ZelTroN-2k3/arduino-cibi-vfo/img/config_menu_06.jpg

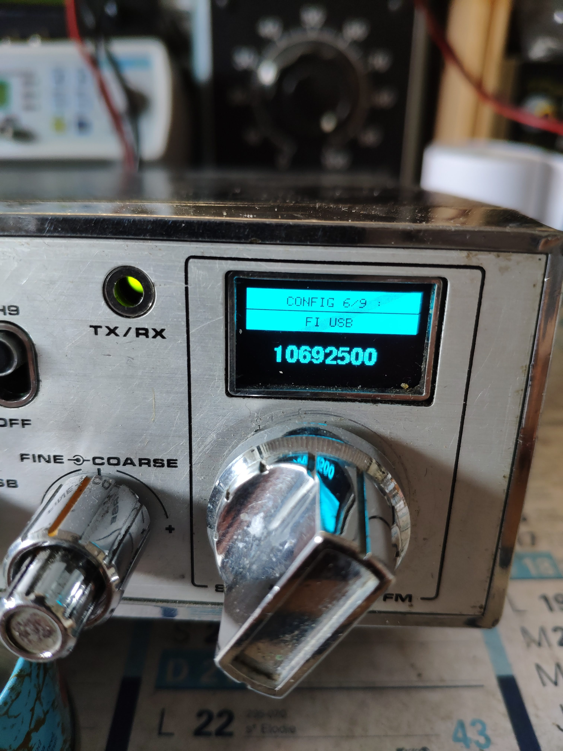
img/config_menu_06.jpg
