ZelTroN-2k3/arduino-cibi-vfo/img/config_menu_07.jpg

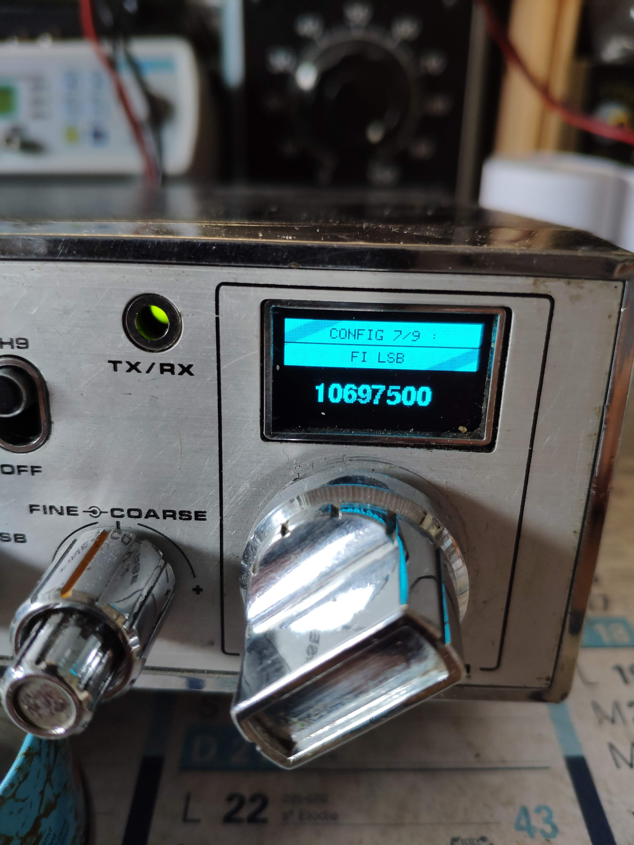
img/config_menu_07.jpg
