ZelTroN-2k3/arduino-cibi-vfo/img/main_menu_clarifier_fine.jpg

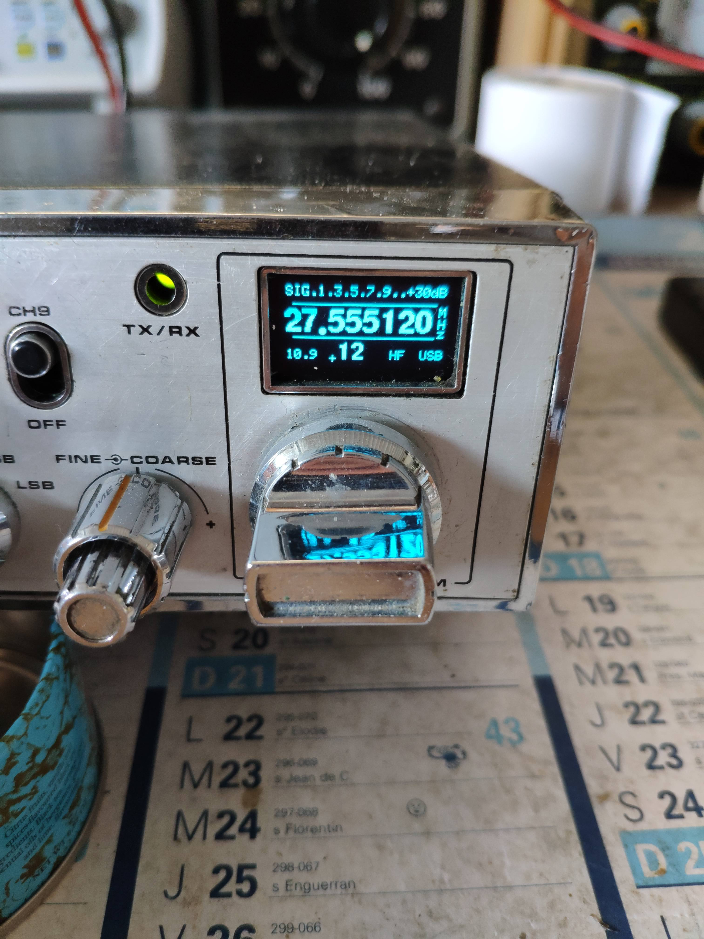
img/main_menu_clarifier_fine.jpg
