ZelTroN-2k3/arduino-cibi-vfo/img/main_menu_smeter_01.jpg

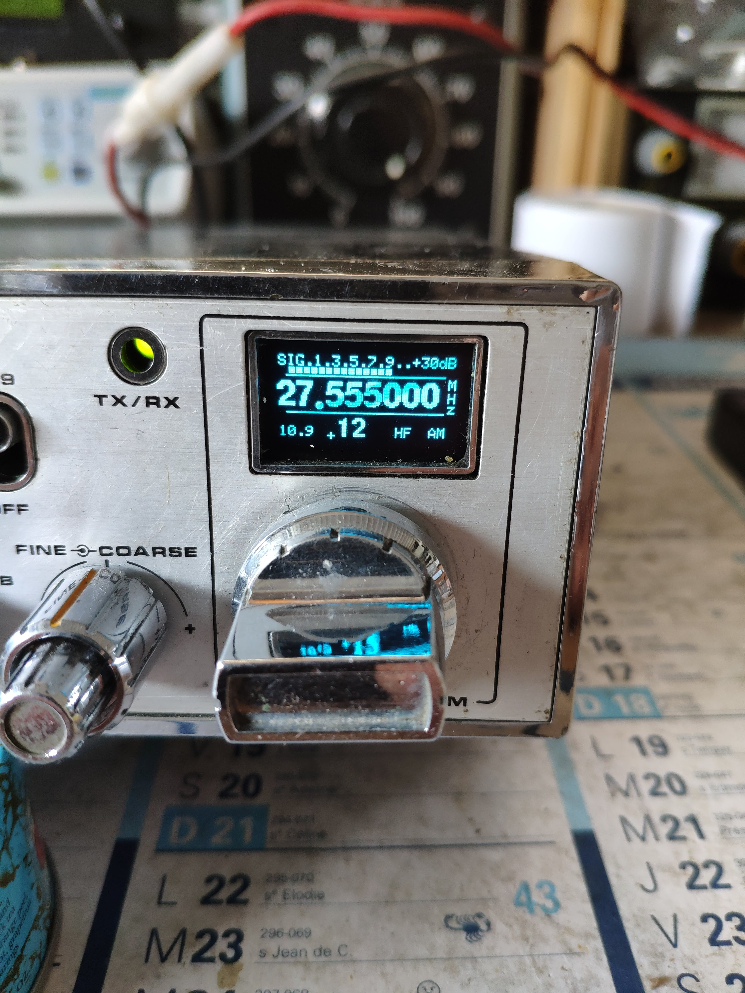
img/main_menu_smeter_01.jpg
