ZelTroN-2k3/arduino-cibi-vfo/img/main_menu_smeter_02.jpg

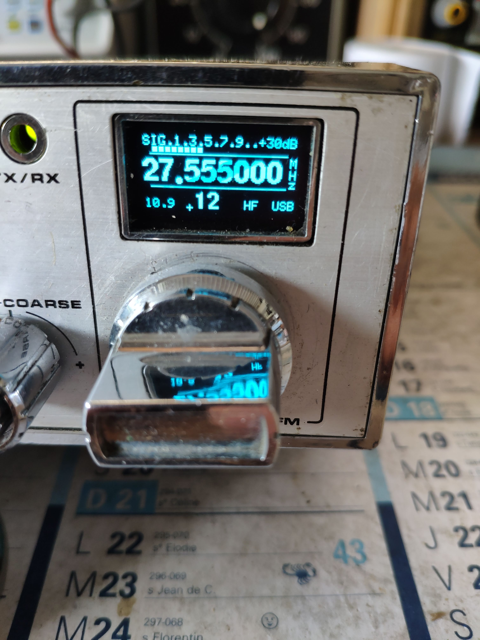
img/main_menu_smeter_02.jpg
