ZelTroN-2k3/arduino-cibi-vfo/src/config.cpp

/*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
 * * Redistributions of source code must retain the above copyright
 *   notice, this list of conditions and the following disclaimer.
 * * Redistributions in binary form must reproduce the above copyright
 *   notice, this list of conditions and the following disclaimer in the
 *   documentation and/or other materials provided with the distribution.
 * * Neither the name of the author Vincent Hervieux, nor the
 *   names of its contributors may be used to endorse or promote products
 *   derived from this software without specific prior written permission.
 *
 * THIS SOFTWARE IS PROVIDED BY THE REGENTS AND CONTRIBUTORS ``AS IS'' AND ANY
 * EXPRESS OR IMPLIED WARRANTIES, INCLUDING, BUT NOT LIMITED TO, THE IMPLIED
 * WARRANTIES OF MERCHANTABILITY AND FITNESS FOR A PARTICULAR PURPOSE ARE
 * DISCLAIMED. IN NO EVENT SHALL THE REGENTS AND CONTRIBUTORS BE LIABLE FOR ANY
 * DIRECT, INDIRECT, INCIDENTAL, SPECIAL, EXEMPLARY, OR CONSEQUENTIAL DAMAGES
 * (INCLUDING, BUT NOT LIMITED TO, PROCUREMENT OF SUBSTITUTE GOODS OR SERVICES;
 * LOSS OF USE, DATA, OR PROFITS; OR BUSINESS INTERRUPTION) HOWEVER CAUSED AND
 * ON ANY THEORY OF LIABILITY, WHETHER IN CONTRACT, STRICT LIABILITY, OR TORT
 * (INCLUDING NEGLIGENCE OR OTHERWISE) ARISING IN ANY WAY OUT OF THE USE OF THIS
 * SOFTWARE, EVEN IF ADVISED OF THE POSSIBILITY OF SUCH DAMAGE.
 */

#include "config.h"
#include "utils.h"
#include "vfo.h"

#include <avr/eeprom.h>

const static uint32_t EEPROM_HEADER         PROGMEM =  0xDEADBEEF;
const static uint32_t DEFAULT_CIBI_FREQ     PROGMEM =  27555000;
const static uint32_t DEFAULT_CIBI_MIN_FREQ PROGMEM =  25000000;
const static uint32_t DEFAULT_CIBI_MAX_FREQ PROGMEM =  30000000;
const static uint32_t DEFAULT_FREQ_STEP_INC PROGMEM =  5000;
/* On superstar 3900 and derivated:
  - reference oscillator is at 10240KHz
  - FI is either 10695KHz(CW,AM,FM), 10692.5KHz(USB), 10697.5KHz(LSB) */
const static uint32_t DEFAULT_FI_FREQ_AM PROGMEM = 10695000;
const static uint32_t DEFAULT_FI_FREQ_USB PROGMEM = 10692500;
const static uint32_t DEFAULT_FI_FREQ_LSB PROGMEM = 10697500;
const static  int32_t DEFAULT_VFO_ADJ PROGMEM = 0; 
const static  int32_t DEFAULT_CLARIFIER_ADJ PROGMEM = 0; 
const static  int32_t DEFAULT_SMETER_ADJ PROGMEM = 0; 
Config::Config(Input &_input, U8G2 &_display, DDS &_dds):
context_({ 
  .eeprom_header = EEPROM_HEADER,
  .cibi_frequency = DEFAULT_CIBI_FREQ,
  .cibi_min_freq = DEFAULT_CIBI_MIN_FREQ,
  .cibi_max_freq = DEFAULT_CIBI_MAX_FREQ,
  .freq_step_inc = DEFAULT_FREQ_STEP_INC,
  .fi_am = DEFAULT_FI_FREQ_AM,
  .fi_usb = DEFAULT_FI_FREQ_USB,
  .fi_lsb = DEFAULT_FI_FREQ_LSB,
  .vfo_adj = DEFAULT_VFO_ADJ,
  .clarifier_adj = DEFAULT_CLARIFIER_ADJ,
  .smeter_adj = DEFAULT_SMETER_ADJ
}),
input_(_input),
dds_(_dds),
current_cursor_pos_(CURSOR_POS_NONE),
current_menu_index_(CONFIG_CIBI_FREQ),
current_value_(&context_.cibi_frequency)
{
  view_ = new ConfigDisplay(_display);
}

Config::Config(const Config& _config) :
context_({ 
  .eeprom_header = _config.context_.eeprom_header,
  .cibi_frequency = _config.context_.cibi_frequency,
  .cibi_min_freq = _config.context_.cibi_min_freq,
  .cibi_max_freq = _config.context_.cibi_max_freq,
  .freq_step_inc = _config.context_.freq_step_inc,
  .fi_am = _config.context_.fi_am,
  .fi_usb = _config.context_.fi_usb,
  .fi_lsb = _config.context_.fi_lsb,
  .vfo_adj = _config.context_.vfo_adj,
  .clarifier_adj = _config.context_.clarifier_adj,
  .smeter_adj = _config.context_.smeter_adj,
}),
input_(_config.input_),
dds_(_config.dds_),
view_(_config.view_),
current_cursor_pos_(_config.current_cursor_pos_),
current_menu_index_(_config.current_menu_index_),
current_value_(_config.current_value_)
{

}

Config::~Config()
{
  delete view_;
}

void Config::loop(bool _update_display)
{
  bool update = _update_display;
  uint32_t freq_step = 0;
  int increment = 0;
  if(input_.buttonClicked())
  {
    update = true;
    current_cursor_pos_++;
    if(current_cursor_pos_ >= CURSOR_POS_MAX)
    {
      current_cursor_pos_ = CURSOR_POS_NONE;
    }
  }
  freq_step = quick_pow10(current_cursor_pos_-1);
  increment = (int)input_.getEncoderIncrement();
  if(increment) 
  {
    update = true;
    if(CURSOR_POS_NONE == current_cursor_pos_)
    {
      /* change between menu items */
      current_menu_index_ += increment;

      if (current_menu_index_ >= CONFIG_MAX)
      {
        current_menu_index_ = 0;
      }
      else if (current_menu_index_ < 0)
      {
        current_menu_index_ = CONFIG_MAX - 1;
      }

      /* change displayed item value */
      switch (current_menu_index_)
      {
        case CONFIG_CIBI_FREQ:
          current_value_ = &context_.cibi_frequency;
          break;
        case CONFIG_CIBI_MIN_FREQ:
          current_value_ = &context_.cibi_min_freq;
          break;
        case CONFIG_CIBI_MAX_FREQ:
          current_value_ = &context_.cibi_max_freq;
          break;
        case CONFIG_FREQ_STEP:
          current_value_ = &context_.freq_step_inc;
          break;
        case CONFIG_FI_AM:
          current_value_ = &context_.fi_am;          /* FI AM/FM/CW */
          break;
        case CONFIG_FI_USB:
          current_value_ = &context_.fi_usb;         /* FI USB */
          break;
        case CONFIG_FI_LSB:
          current_value_ = &context_.fi_lsb;         /* FI LSB */
          break;
        case CONFIG_VFO_ADJ:     
          current_value_ = (uint32_t*)&context_.vfo_adj;
          break;
        case CONFIG_CLARIFIER_ADJ:     
          current_value_ = (uint32_t*)&context_.clarifier_adj;
          break;
        case CONFIG_SMETER_ADJ:
          current_value_ = (uint32_t*)&context_.smeter_adj;
          break;
        default:
          return;
      }
    }
    else
    {
      if((current_menu_index_ != CONFIG_VFO_ADJ) && 
         (current_menu_index_ != CONFIG_CLARIFIER_ADJ) && 
         (current_menu_index_ != CONFIG_SMETER_ADJ) && 
         (increment < 0) && 
         (freq_step * abs(increment)) > (*current_value_))
      {
          /* avoid negative values */
          (*current_value_) = 0;
      }
      else
      {
          (*current_value_) += ((uint32_t)increment * freq_step);
      }
    }
  }

  if(update)
  {
    view_->clear();

    if(CURSOR_POS_NONE == current_cursor_pos_)
    {
      view_->highlightTitle(WHITE);
      view_->setTitle(current_menu_index_, BLACK);
    }
    else
    {
      view_->setTitle(current_menu_index_, WHITE);
    }
    
    if (current_menu_index_ != CONFIG_VFO_ADJ &&
        current_menu_index_ != CONFIG_CLARIFIER_ADJ &&
        current_menu_index_ != CONFIG_SMETER_ADJ)
    {
      view_->setValueUint((*current_value_), WHITE);
    }
    else
    {
      view_->setValueInt((*(int32_t*)current_value_), WHITE);
    }

    if(current_menu_index_ == CONFIG_VFO_ADJ)
    {
      /* set si5351 correction here */
      dds_.setOutputCorrection((*(int32_t*)current_value_));
    }
    
    view_->setCursorPos(current_cursor_pos_, WHITE);
    view_->display();
  }
}

int Config::open()
{
  eeprom_read_block((void*)&context_, (void*)0, sizeof(context_t));
  if(context_.eeprom_header != EEPROM_HEADER) 
  {
    /* EEPROM first time use */
    context_.eeprom_header = EEPROM_HEADER;
    context_.cibi_frequency = DEFAULT_CIBI_FREQ;
    context_.cibi_min_freq = DEFAULT_CIBI_MIN_FREQ;
    context_.cibi_max_freq = DEFAULT_CIBI_MAX_FREQ;
    context_.freq_step_inc = DEFAULT_FREQ_STEP_INC;
    context_.fi_am = DEFAULT_FI_FREQ_AM;
    context_.fi_usb = DEFAULT_FI_FREQ_USB;
    context_.fi_lsb = DEFAULT_FI_FREQ_LSB;
    context_.vfo_adj = DEFAULT_VFO_ADJ;
    context_.smeter_adj = DEFAULT_SMETER_ADJ;
  }
  return 0;
}

int Config::save()
{
  eeprom_update_block((const void*)&context_, (void*)0, sizeof(context_t));
  return 0;
}

const uint32_t& Config::getCibiFreq()
{
  return context_.cibi_frequency;
}

const uint32_t& Config::getCibiMinFreq()
{
  return context_.cibi_min_freq;
}

const uint32_t& Config::getCibiMaxFreq()
{
  return context_.cibi_max_freq;
}

const uint32_t& Config::getFreqStepIncrement()
{
  return  context_.freq_step_inc;
}

const uint32_t& Config::getFiAm()
{
  return context_.fi_am;
}

const uint32_t& Config::getFiUsb()
{
  return context_.fi_usb;
}

const uint32_t& Config::getFiLsb()
{
  return context_.fi_lsb;
}

const int32_t& Config::getVFOAdj()
{
  return context_.vfo_adj;
}

const int32_t& Config::getClarifierAdj()
{
  return context_.clarifier_adj;
}

const int32_t& Config::getSMeterAdj()
{
  return context_.smeter_adj;
}

void Config::setCibiFreq(const uint32_t& _freq)
{
  if(_freq != context_.cibi_frequency)
  {
    context_.cibi_frequency = _freq;
    save();
  }
}
